talla83/tshw-parport/LinuxCNC-tshw-parport/my-mill/my-mill.ini

# Generated by stepconf 1.1 at Sun Dec 27 16:18:48 2020
# Änderungen an dieser Datei werden beim nächsten
# overwritten when you run stepconf again

[EMC]
MACHINE = my-mill
DEBUG = 0
VERSION = 1.1

[DISPLAY]
DISPLAY = axis
EDITOR = gedit
POSITION_OFFSET = RELATIVE
POSITION_FEEDBACK = ACTUAL
ARCDIVISION = 64
GRIDS = 10mm 20mm 50mm 100mm 1in 2in 5in 10in
MAX_FEED_OVERRIDE = 1.2
MIN_SPINDLE_OVERRIDE = 0.5
MAX_SPINDLE_OVERRIDE = 1.2
DEFAULT_LINEAR_VELOCITY = 5.00
MIN_LINEAR_VELOCITY = 0
MAX_LINEAR_VELOCITY = 50.00
INTRO_GRAPHIC = linuxcnc.gif
INTRO_TIME = 5
PROGRAM_PREFIX = /home/cnc/linuxcnc/nc_files
INCREMENTS = 5mm 1mm .5mm .1mm .05mm .01mm .005mm

[KINS]
JOINTS = 3
KINEMATICS = trivkins coordinates=XYZ

[FILTER]
PROGRAM_EXTENSION = .png,.gif,.jpg Greyscale Depth Image
PROGRAM_EXTENSION = .py Python Script
PROGRAM_EXTENSION = .nc,.tap G-Code File
png = image-to-gcode
gif = image-to-gcode
jpg = image-to-gcode
py = python

[TASK]
TASK = milltask
CYCLE_TIME = 0.010

[RS274NGC]
PARAMETER_FILE = linuxcnc.var

[EMCMOT]
EMCMOT = motmod
COMM_TIMEOUT = 1.0
BASE_PERIOD = 100000
SERVO_PERIOD = 1000000

[HAL]
HALUI = halui
HALFILE = my-mill.hal
HALFILE = custom.hal
POSTGUI_HALFILE = postgui_call_list.hal

[HALUI]
MDI_COMMAND = G10 L20 P1 X0
MDI_COMMAND = G10 L20 P1 Y0
MDI_COMMAND = G10 L20 P1 Z0

[TRAJ]
COORDINATES =  X Y Z
LINEAR_UNITS = mm
ANGULAR_UNITS = degree
DEFAULT_LINEAR_VELOCITY = 5.00
MAX_LINEAR_VELOCITY = 50.00

[EMCIO]
EMCIO = io
CYCLE_TIME = 0.100
TOOL_TABLE = tool.tbl

[AXIS_X]
MAX_VELOCITY = 47.5
MAX_ACCELERATION = 1000.0
MIN_LIMIT = -0.001
MAX_LIMIT = 120.0

[JOINT_0]
TYPE = LINEAR
HOME = 0.0
MIN_LIMIT = -0.001
MAX_LIMIT = 120.0
MAX_VELOCITY = 47.5
MAX_ACCELERATION = 1000.0
STEPGEN_MAXACCEL = 1250.0
SCALE = 200.0
FERROR = 1
MIN_FERROR = .25
HOME_OFFSET = 8.000000
HOME_SEARCH_VEL = -10.500000
HOME_LATCH_VEL = -1.500000
HOME_SEQUENCE = 1

[AXIS_Y]
MAX_VELOCITY = 47.5
MAX_ACCELERATION = 1000.0
MIN_LIMIT = -0.001
MAX_LIMIT = 120.0

[JOINT_1]
TYPE = LINEAR
HOME = 0.0
MIN_LIMIT = -0.001
MAX_LIMIT = 120.0
MAX_VELOCITY = 47.5
MAX_ACCELERATION = 1000.0
STEPGEN_MAXACCEL = 1250.0
SCALE = 200.0
FERROR = 1
MIN_FERROR = .25
HOME_OFFSET = 8.000000
HOME_SEARCH_VEL = -10.500000
HOME_LATCH_VEL = -1.500000
HOME_SEQUENCE = 2

[AXIS_Z]
MAX_VELOCITY = 47.5
MAX_ACCELERATION = 1000.0
MIN_LIMIT = -100.0
MAX_LIMIT = 0.001

[JOINT_2]
TYPE = LINEAR
HOME = 0.0
MIN_LIMIT = -100.0
MAX_LIMIT = 0.001
MAX_VELOCITY = 47.5
MAX_ACCELERATION = 1000.0
STEPGEN_MAXACCEL = 1250.0
SCALE = 200.0
FERROR = 1
MIN_FERROR = .25
HOME_OFFSET = 0.000000
HOME_SEARCH_VEL = 10.500000
HOME_LATCH_VEL = 1.500000
HOME_SEQUENCE = 0
